4x1md/analog_esr_meter/ltspice/esr_meter.asc

C1: cap; 0.001µ; V=16 Irms=55.6m Rser=5.11126 Lser=0 mfg="KEMET" pn="C0603C102K4RAC" type="X7R"
C2: cap; 0.1µ; V=10 Irms=728m Rser=0.14361 Lser=0 mfg="KEMET" pn="C0603C104K8RAC" type="X7R"
C3: cap; 1µ; V=10 Irms=2.59 Rser=0.0171188 Lser=0 mfg="KEMET" pn="C0603C105K8RAC" type="X7R"
D1: diode; 1N4148
Q1: npn; BC547B
Q2: pnp; BC556B
R1: EuropeanResistor; 68K; tol=1 pwr=0.1
R2: EuropeanResistor; 12K; tol=1 pwr=0.1
R3: EuropeanResistor; 10K; tol=1 pwr=0.1
R4: EuropeanResistor; 1.5K; tol=1 pwr=0.1
R5: EuropeanResistor; 10K; tol=1 pwr=0.1
R6: EuropeanResistor; 4.7K; tol=1 pwr=0.1
R7: EuropeanResistor; 1K; tol=1 pwr=0.1
R8: EuropeanResistor; 22; tol=1 pwr=0.1
R9: EuropeanResistor; 1K; tol=1 pwr=0.1
R10: EuropeanResistor; 22; tol=1 pwr=0.1
R11: EuropeanResistor; 1K; tol=1 pwr=0.1
R12: EuropeanResistor; 1K; tol=1 pwr=0.1
R13: EuropeanResistor; 47K; tol=1 pwr=0.1
R14: EuropeanResistor; 47K; tol=1 pwr=0.1
R15: EuropeanResistor; 47K; tol=1 pwr=0.1
R16: EuropeanResistor; 47; tol=1 pwr=0.1
R17: EuropeanResistor; 10K; tol=1 pwr=0.1
U1: ADTL082
U2: ADTL082
U3: ADTL082
V1: voltage; 4.5V
V2: voltage; 4.5V
Named nets: +4.5V, -4.5V, 0, osc, Vc, bridge, OUT, amp_out, amp+, amp-
.tran 25m startup
